FunKey-Project/FunKey-S-Hardware/shapes3D/CRYSTAL-3225.step

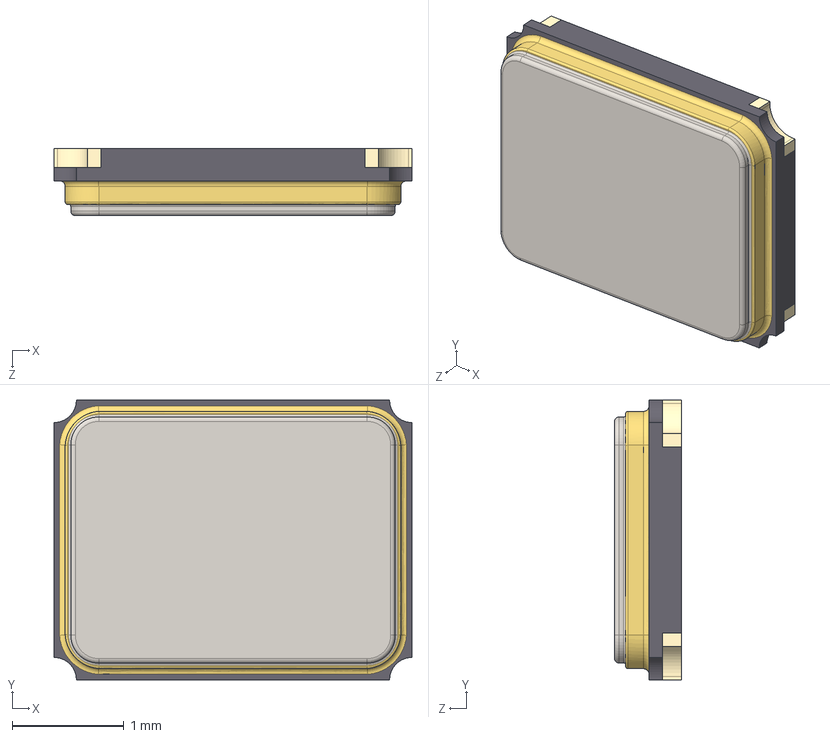
[picture p18: CAD file, 2020-11-29]
shapes3D/CRYSTAL-3225.step
3.20 x 2.50 x 0.6 mm
